ppusapati/weather/firmware/src/error.rs

/// Unified error type for the weather station firmware.

use core::fmt;

#[derive(Debug, Clone, Copy, PartialEq, Eq)]
pub enum Error {
    // Sensor errors
    SensorNotFound(SensorKind),
    SensorReadFailed(SensorKind),
    SensorOutOfRange(SensorKind),
    SensorDegraded(SensorKind),

    // WiFi module errors (ATWINC1500)
    WifiModuleInitFailed,
    WifiModuleNotResponding,
    WifiConnectionFailed,
    WifiTimeout,
    WifiScanFailed,

    // MQTT errors
    MqttConnectionFailed,
    MqttPublishFailed,
    MqttSubscribeFailed,

    // BLE module errors (RN4870)
    BleInitFailed,
    BleAdvertiseFailed,
    BleConnectionFailed,
    BleNotReady,

    // LoRa errors
    LoraInitFailed,
    LoraTxFailed,
    LoraRxTimeout,

    // HTTP errors
    HttpServerError,

    // Cellular errors (SIM7600)
    #[cfg(feature = "cellular")]
    CellularInitFailed,
    #[cfg(feature = "cellular")]
    CellularNoSignal,
    #[cfg(feature = "cellular")]
    CellularRegistrationFailed,
    #[cfg(feature = "cellular")]
    CellularTxFailed,
    #[cfg(feature = "cellular")]
    CellularSimError,
    #[cfg(feature = "cellular")]
    CellularDataConnectionFailed,
    #[cfg(feature = "cellular")]
    CellularTimeout,

    // Ethernet errors (W5500)
    #[cfg(feature = "ethernet")]
    EthernetInitFailed,
    #[cfg(feature = "ethernet")]
    EthernetLinkDown,
    #[cfg(feature = "ethernet")]
    EthernetDhcpFailed,
    #[cfg(feature = "ethernet")]
    EthernetSocketError,
    #[cfg(feature = "ethernet")]
    EthernetTxFailed,

    // I2C / SPI bus errors
    I2cNack,
    I2cBusError,
    I2cTimeout,
    SpiBusError,
    SpiTimeout,

    // Storage errors
    FlashWriteFailed,
    FlashReadFailed,
    FlashFull,
    NvsError,

    // SD card errors
    #[cfg(feature = "sdcard")]
    SdCardNotInserted,
    #[cfg(feature = "sdcard")]
    SdCardInitFailed,
    #[cfg(feature = "sdcard")]
    SdCardWriteFailed,
    #[cfg(feature = "sdcard")]
    SdCardReadFailed,
    #[cfg(feature = "sdcard")]
    SdCardFull,

    // OTA errors
    OtaDownloadFailed,
    OtaVerifyFailed,
    OtaFlashFailed,

    // System errors
    OutOfMemory,
    WatchdogTimeout,
    InvalidConfig,
    CrcMismatch,

    // Sensor lifecycle
    SensorNotReady,

    // SCADA / Modbus errors
    ModbusFrameError,
    ModbusCrcError,
    Rs485TxFailed,

    // TCP socket errors
    SocketOpenFailed,
    SocketClosed,
    SocketTimeout,
}

#[derive(Debug, Clone, Copy, PartialEq, Eq)]
pub enum SensorKind {
    Bme280,
    WindSpeed,
    WindDirection,
    RainGauge,
    UvIndex,
    AmbientLight,
    Battery,
    Temperature,
    SoilMoisture,
    SoilTemperature,
    LeafWetness,
    Pyranometer,
    PanelTemperature,
    Pm25,
}

impl fmt::Display for Error {
    fn fmt(&self, f: &mut fmt::Formatter<'_>) -> fmt::Result {
        match self {
            Error::SensorNotFound(s) => write!(f, "sensor not found: {:?}", s),
            Error::SensorReadFailed(s) => write!(f, "sensor read failed: {:?}", s),
            Error::SensorOutOfRange(s) => write!(f, "sensor out of range: {:?}", s),
            Error::SensorDegraded(s) => write!(f, "sensor degraded: {:?}", s),
            Error::WifiModuleInitFailed => write!(f, "WiFi module init failed"),
            Error::WifiModuleNotResponding => write!(f, "WiFi module not responding"),
            Error::WifiConnectionFailed => write!(f, "WiFi connection failed"),
            Error::WifiTimeout => write!(f, "WiFi timeout"),
            Error::WifiScanFailed => write!(f, "WiFi scan failed"),
            Error::BleInitFailed => write!(f, "BLE module init failed"),
            Error::BleAdvertiseFailed => write!(f, "BLE advertise failed"),
            Error::BleConnectionFailed => write!(f, "BLE connection failed"),
            Error::BleNotReady => write!(f, "BLE module not ready"),
            Error::MqttConnectionFailed => write!(f, "MQTT connection failed"),
            Error::MqttPublishFailed => write!(f, "MQTT publish failed"),
            Error::MqttSubscribeFailed => write!(f, "MQTT subscribe failed"),
            Error::LoraInitFailed => write!(f, "LoRa init failed"),
            Error::LoraTxFailed => write!(f, "LoRa TX failed"),
            Error::LoraRxTimeout => write!(f, "LoRa RX timeout"),
            Error::HttpServerError => write!(f, "HTTP server error"),
            #[cfg(feature = "cellular")]
            Error::CellularInitFailed => write!(f, "cellular init failed"),
            #[cfg(feature = "cellular")]
            Error::CellularNoSignal => write!(f, "cellular no signal"),
            #[cfg(feature = "cellular")]
            Error::CellularRegistrationFailed => write!(f, "cellular registration failed"),
            #[cfg(feature = "cellular")]
            Error::CellularTxFailed => write!(f, "cellular TX failed"),
            #[cfg(feature = "cellular")]
            Error::CellularSimError => write!(f, "SIM card error"),
            #[cfg(feature = "cellular")]
            Error::CellularDataConnectionFailed => write!(f, "cellular data connection failed"),
            #[cfg(feature = "cellular")]
            Error::CellularTimeout => write!(f, "cellular timeout"),
            #[cfg(feature = "ethernet")]
            Error::EthernetInitFailed => write!(f, "Ethernet init failed"),
            #[cfg(feature = "ethernet")]
            Error::EthernetLinkDown => write!(f, "Ethernet link down"),
            #[cfg(feature = "ethernet")]
            Error::EthernetDhcpFailed => write!(f, "Ethernet DHCP failed"),
            #[cfg(feature = "ethernet")]
            Error::EthernetSocketError => write!(f, "Ethernet socket error"),
            #[cfg(feature = "ethernet")]
            Error::EthernetTxFailed => write!(f, "Ethernet TX failed"),
            Error::I2cNack => write!(f, "I2C NACK"),
            Error::I2cBusError => write!(f, "I2C bus error"),
            Error::I2cTimeout => write!(f, "I2C timeout"),
            Error::SpiBusError => write!(f, "SPI bus error"),
            Error::SpiTimeout => write!(f, "SPI timeout"),
            Error::FlashWriteFailed => write!(f, "flash write failed"),
            Error::FlashReadFailed => write!(f, "flash read failed"),
            Error::FlashFull => write!(f, "flash storage full"),
            Error::NvsError => write!(f, "NVS error"),
            #[cfg(feature = "sdcard")]
            Error::SdCardNotInserted => write!(f, "SD card not inserted"),
            #[cfg(feature = "sdcard")]
            Error::SdCardInitFailed => write!(f, "SD card init failed"),
            #[cfg(feature = "sdcard")]
            Error::SdCardWriteFailed => write!(f, "SD card write failed"),
            #[cfg(feature = "sdcard")]
            Error::SdCardReadFailed => write!(f, "SD card read failed"),
            #[cfg(feature = "sdcard")]
            Error::SdCardFull => write!(f, "SD card full"),
            Error::OtaDownloadFailed => write!(f, "OTA download failed"),
            Error::OtaVerifyFailed => write!(f, "OTA verify failed"),
            Error::OtaFlashFailed => write!(f, "OTA flash failed"),
            Error::OutOfMemory => write!(f, "out of memory"),
            Error::WatchdogTimeout => write!(f, "watchdog timeout"),
            Error::InvalidConfig => write!(f, "invalid configuration"),
            Error::CrcMismatch => write!(f, "CRC mismatch"),
            Error::SensorNotReady => write!(f, "sensor not ready"),
            Error::ModbusFrameError => write!(f, "Modbus frame error"),
            Error::ModbusCrcError => write!(f, "Modbus CRC error"),
            Error::Rs485TxFailed => write!(f, "RS485 transmit failed"),
            Error::SocketOpenFailed => write!(f, "TCP socket open failed"),
            Error::SocketClosed => write!(f, "TCP socket closed"),
            Error::SocketTimeout => write!(f, "TCP socket timeout"),
        }
    }
}

impl fmt::Display for SensorKind {
    fn fmt(&self, f: &mut fmt::Formatter<'_>) -> fmt::Result {
        match self {
            SensorKind::Bme280 => write!(f, "BME280"),
            SensorKind::WindSpeed => write!(f, "Wind Speed"),
            SensorKind::WindDirection => write!(f, "Wind Direction"),
            SensorKind::RainGauge => write!(f, "Rain Gauge"),
            SensorKind::UvIndex => write!(f, "UV Index"),
            SensorKind::AmbientLight => write!(f, "Ambient Light"),
            SensorKind::Battery => write!(f, "Battery"),
            SensorKind::Temperature => write!(f, "Temperature"),
            SensorKind::SoilMoisture => write!(f, "Soil Moisture"),
            SensorKind::SoilTemperature => write!(f, "Soil Temperature"),
            SensorKind::LeafWetness => write!(f, "Leaf Wetness"),
            SensorKind::Pyranometer => write!(f, "Pyranometer"),
            SensorKind::PanelTemperature => write!(f, "Panel Temperature"),
            SensorKind::Pm25 => write!(f, "PM2.5"),
        }
    }
}

pub type Result<T> = core::result::Result<T, Error>;
